PMilstone/Kolbe-Customs-Controller/Pictures/IMG_4933.jpg

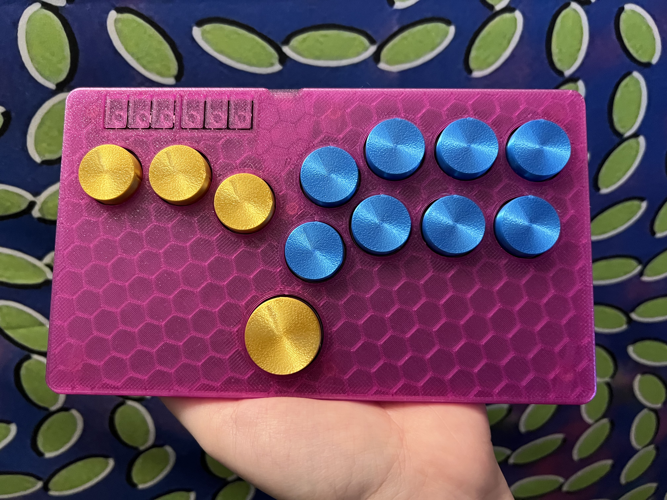
Pictures/IMG_4933.jpg
