PMilstone/Kolbe-Customs-Controller/Pictures/IMG_5112.jpg

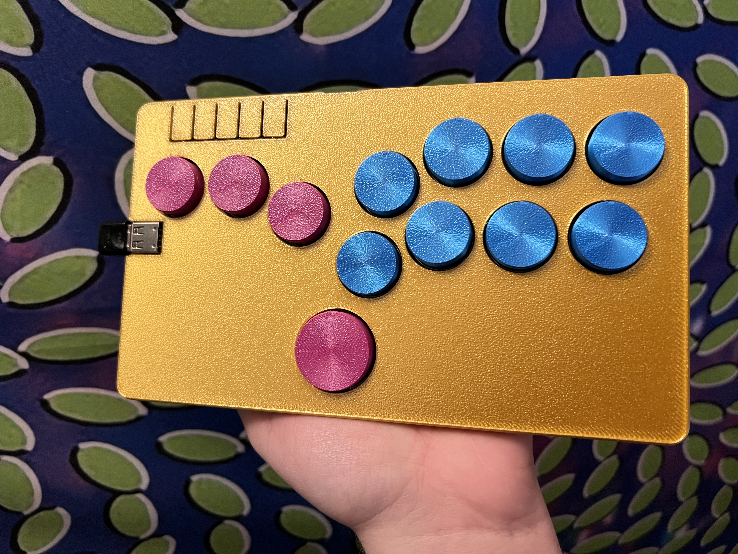
Pictures/IMG_5112.jpg
