PMilstone/Kolbe-Customs-Controller/Pictures/IMG_5122.jpg

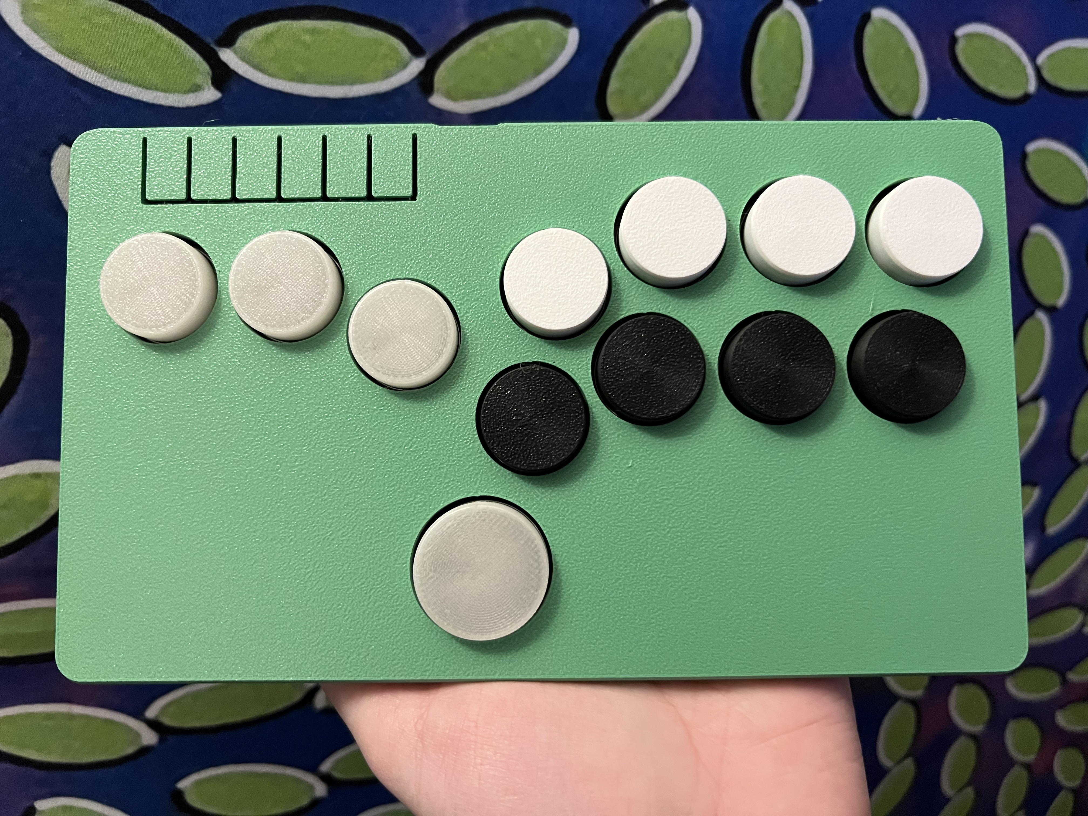
Pictures/IMG_5122.jpg
