PMilstone/Kolbe-Customs-Controller/Pictures/IMG_5352.jpg

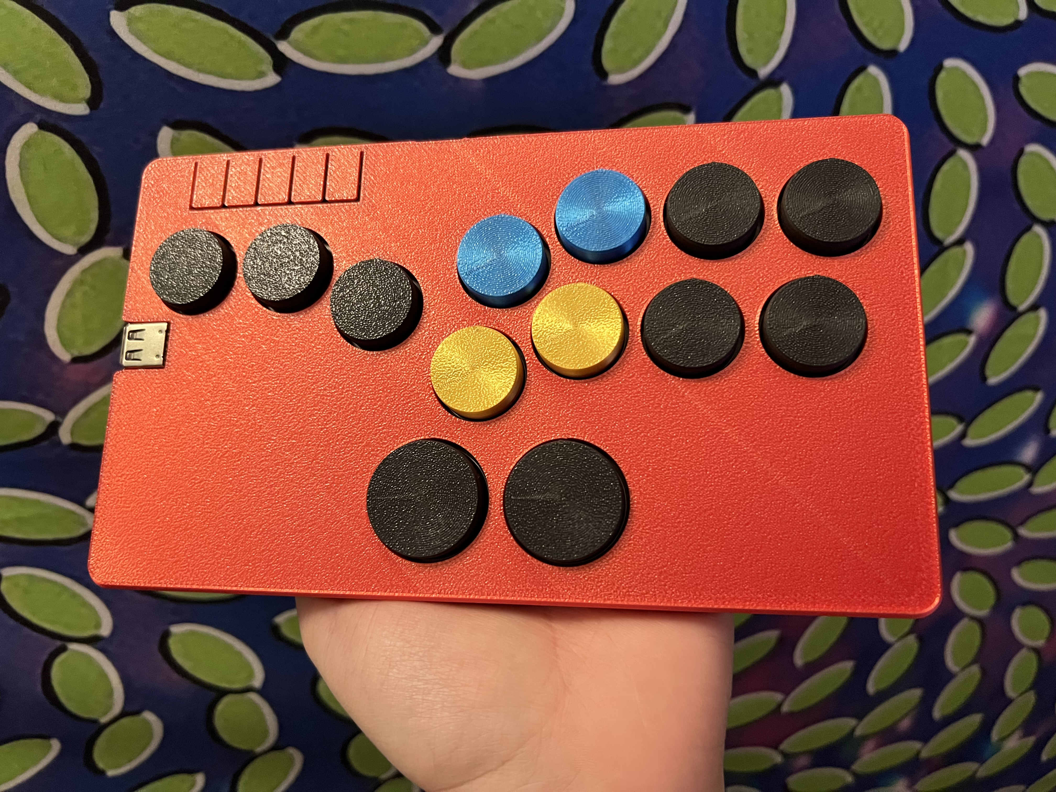
Pictures/IMG_5352.jpg
