PMilstone/Kolbe-Customs-Controller/Pictures/IMG_5424.jpg

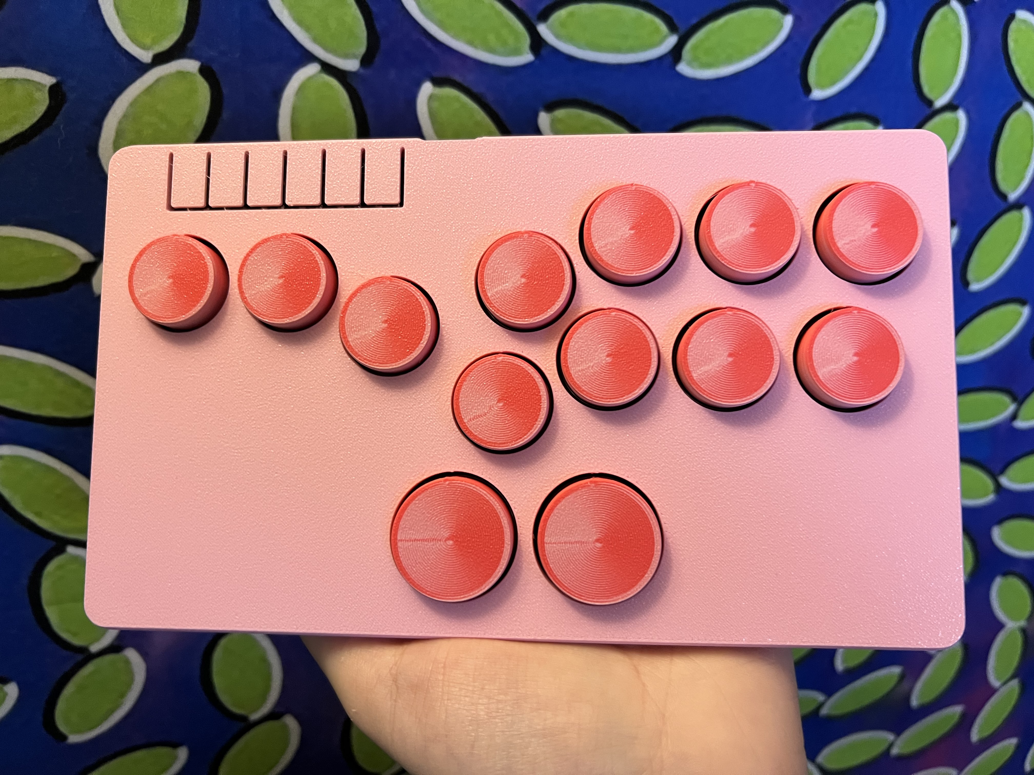
Pictures/IMG_5424.jpg
